Mark-RT/BrainRing_Wireless/3D/Admin/кнопка розміри.png

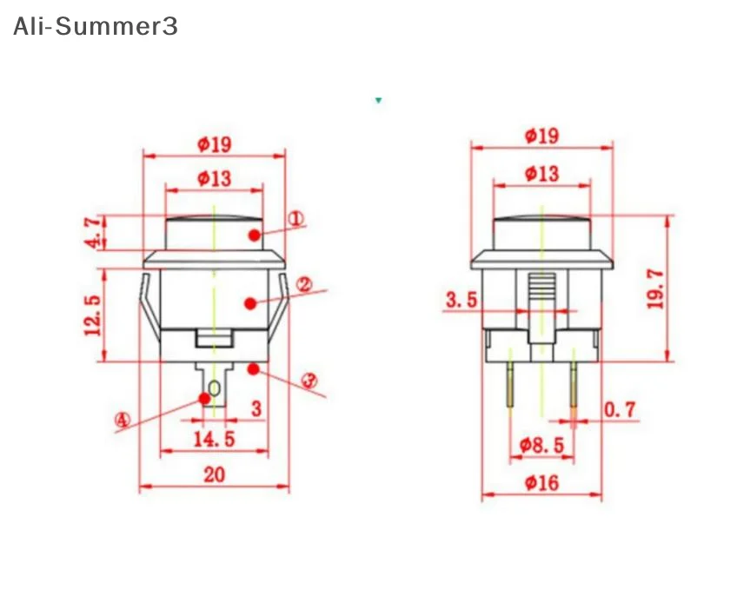
3D/Admin/кнопка розміри.png
