Mark-RT/BrainRing_Wireless/3D/Players/аркадна кнопка розміри.png

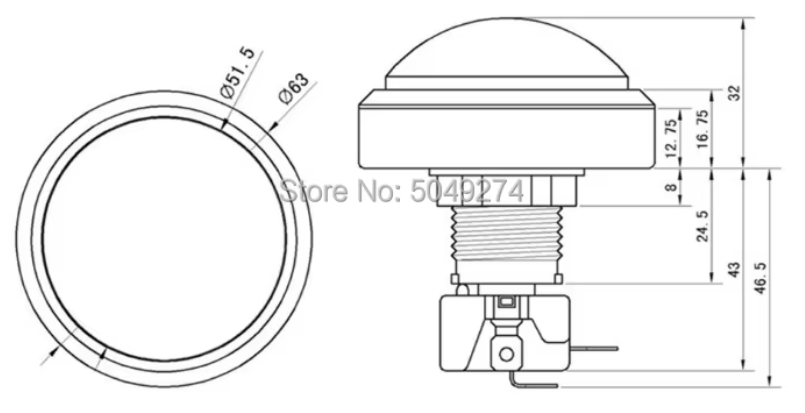
3D/Players/аркадна кнопка розміри.png
