Mark-RT/BrainRing_Wireless/images/IMG_20231107_215259_8.4.300.jpg

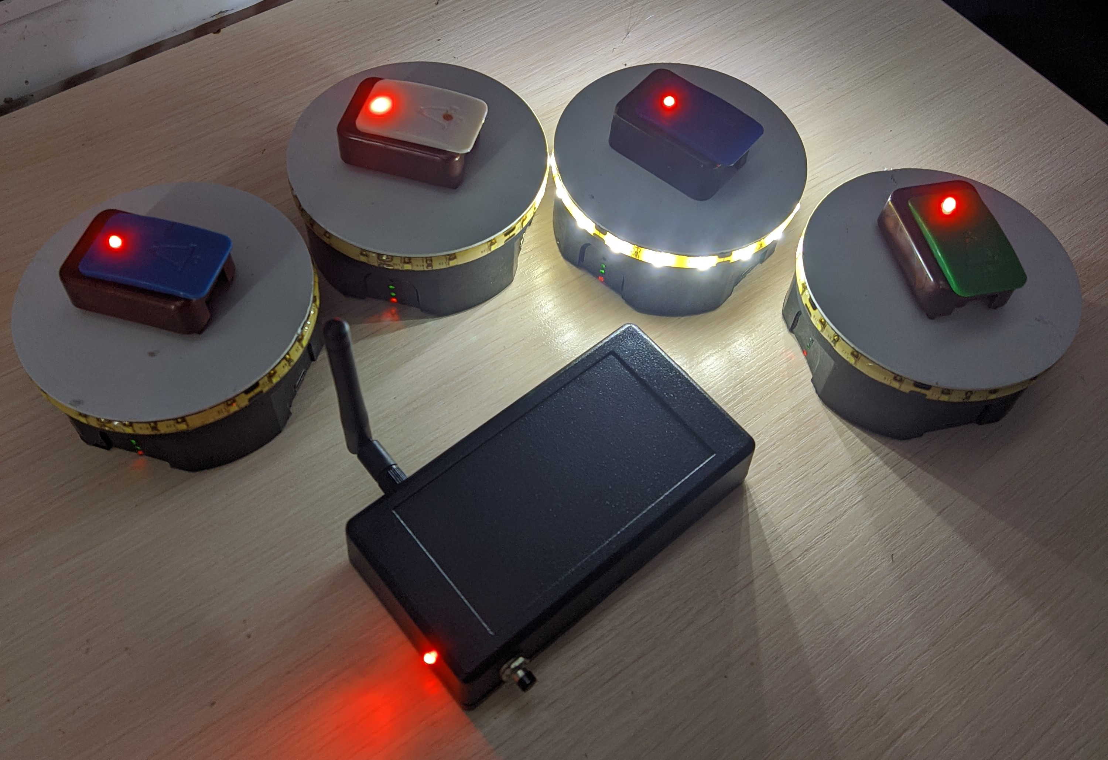
images/IMG_20231107_215259_8.4.300.jpg
