Mark-RT/BrainRing_Wireless/мусор, неудачные попытки/Admin_bb.jpg

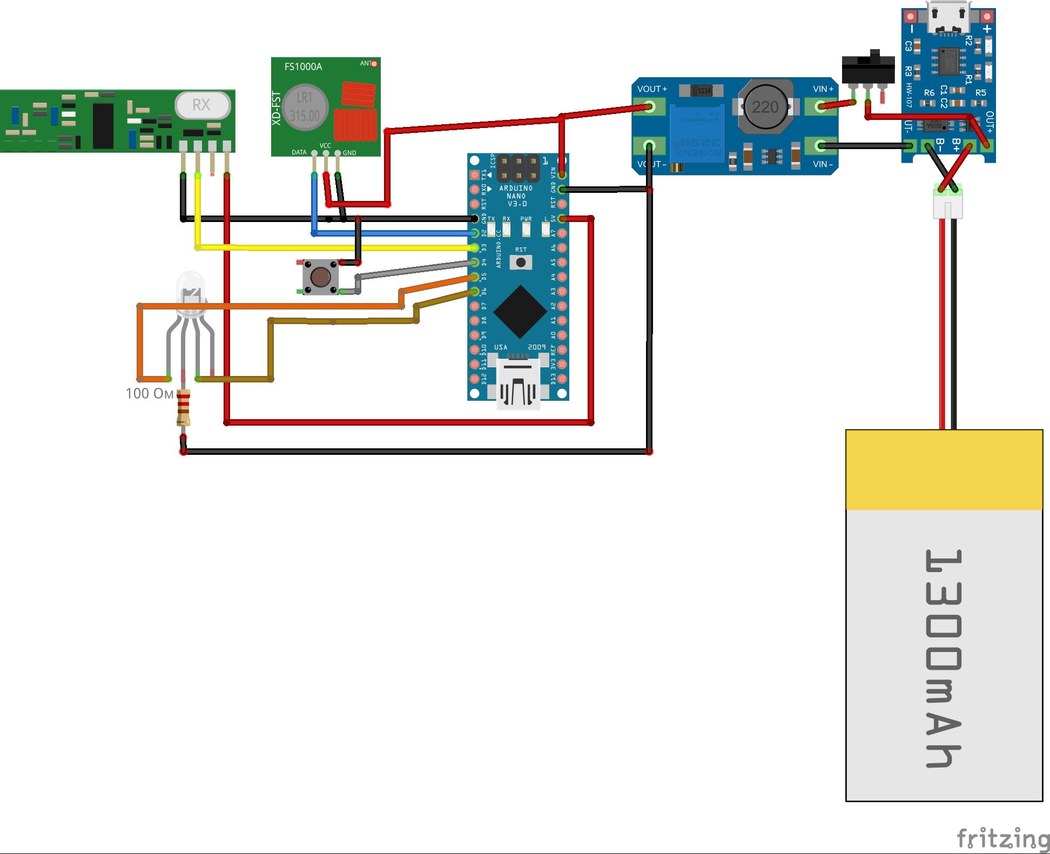
мусор, неудачные попытки/Admin_bb.jpg
