Mark-RT/BrainRing_Wireless/мусор, неудачные попытки/Players (1-4)_bb.jpg

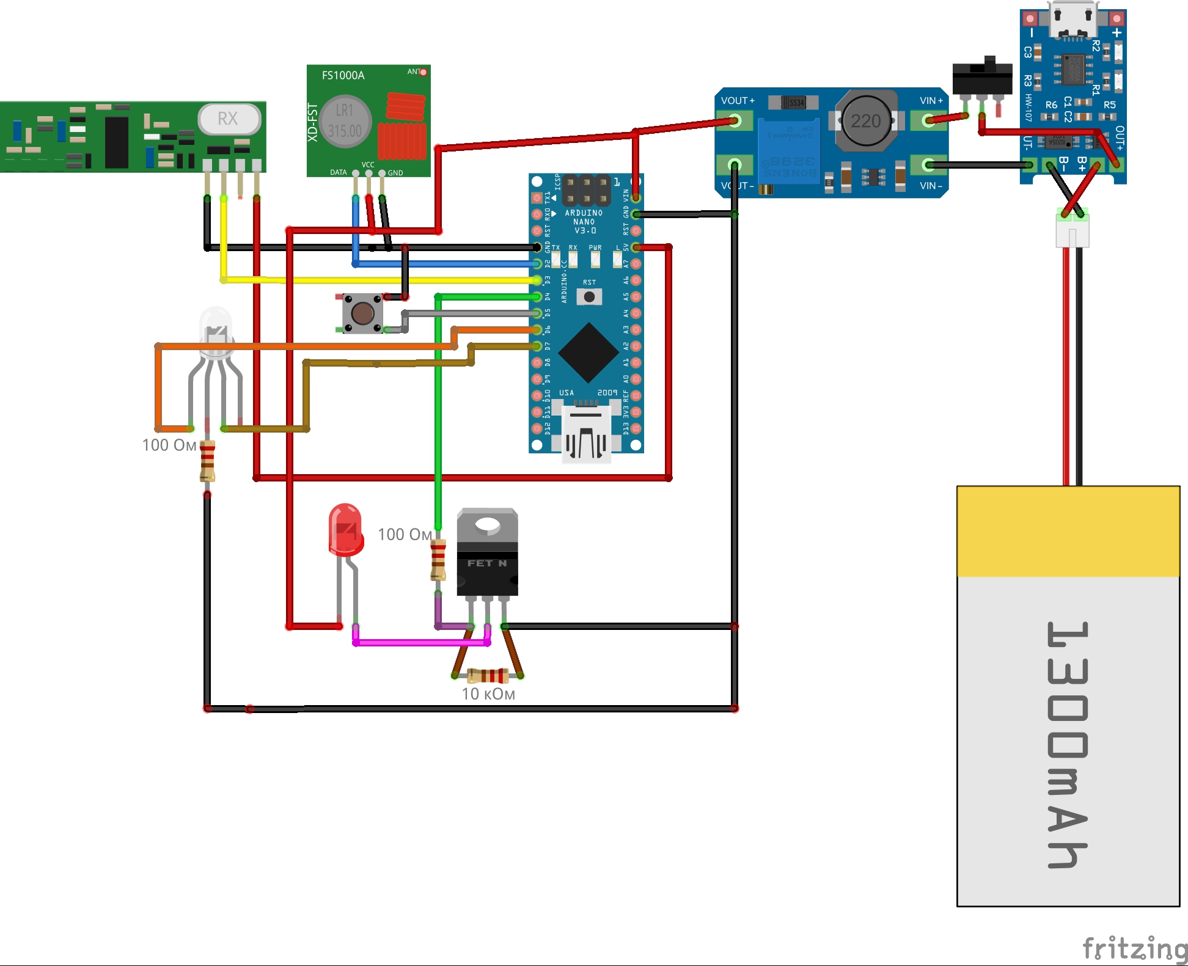
мусор, неудачные попытки/Players (1-4)_bb.jpg
